vjeko2404/Terrarium-dimmable-light-control/Software/ESP_01/2_atmega.ino

// *********************************************************************
// Befehle vom Atmega ausgelesen
// *********************************************************************
void atmega_read() 
// *********************************************************************
{
  atmega = Serial.readString();
  atmega.trim();
}
